SupraCoNeX/SupraCoNeX_3D_outdoor_enclosure_OpenWrt_Router/src/step/scnx_pigtail_bracket_9hole.step

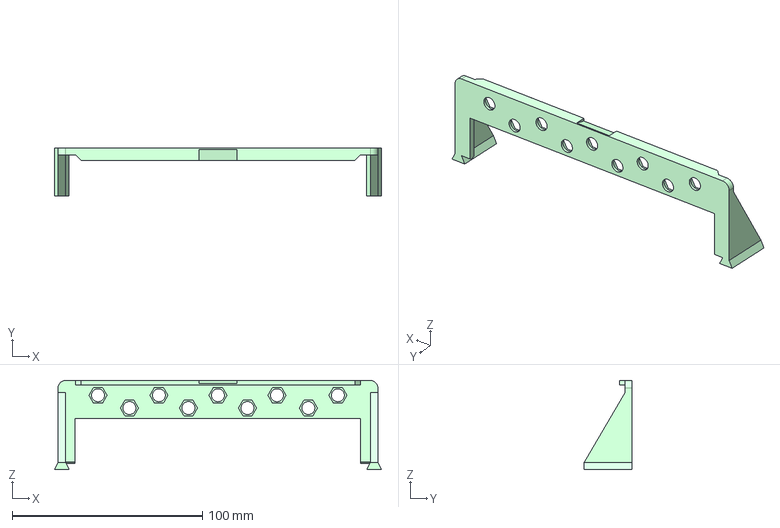
[picture p15: CAD file, 2021-03-08]
src/step/scnx_pigtail_bracket_9hole.step
171.8 x 25.0 x 46.8 mm
