SupraCoNeX/SupraCoNeX_3D_outdoor_enclosure_OpenWrt_Router/src/3mf/scnx_housing_ Boden_2.1_reinforced_pole_triangles.3mf

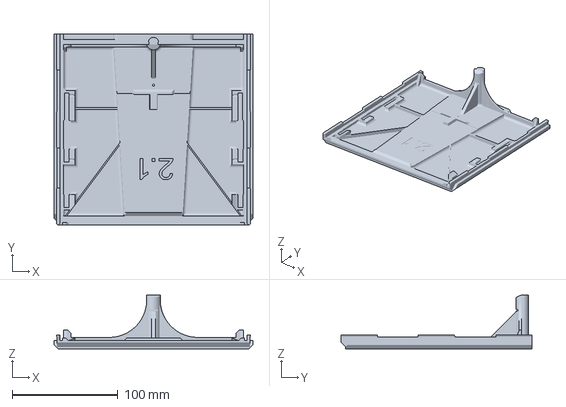
[picture p16: CAD file, 2023-10-01]
src/3mf/scnx_housing_ Boden_2.1_reinforced_pole_triangles.3mf
188.0 x 180.0 x 51.0 mm
