SupraCoNeX/SupraCoNeX_3D_outdoor_enclosure_OpenWrt_Router/src/3mf/scnx_internal_antenna_table_ears.3mf

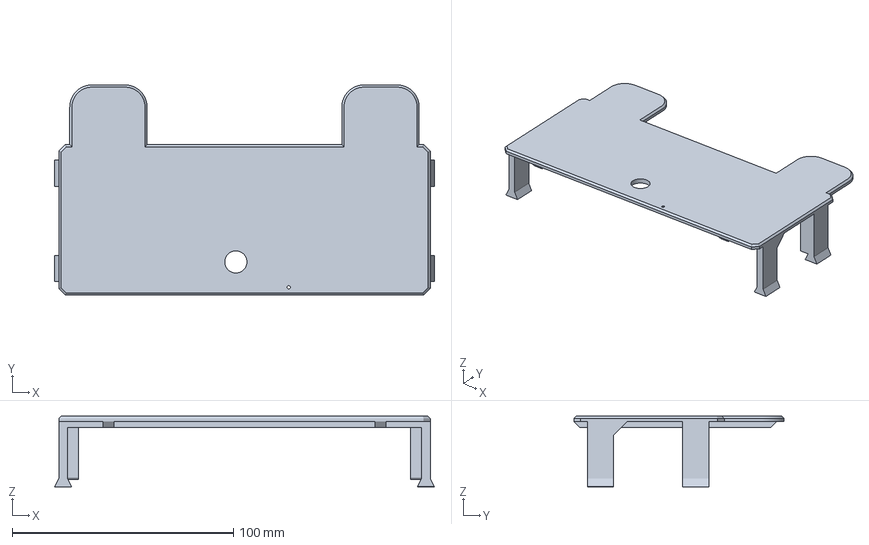
[picture p17: CAD file, 2023-04-04]
src/3mf/scnx_internal_antenna_table_ears.3mf
171.8 x 95.0 x 31.9 mm
