SupraCoNeX/SupraCoNeX_3D_outdoor_enclosure_OpenWrt_Router/src/step/scnx_internal_antenna_table.step

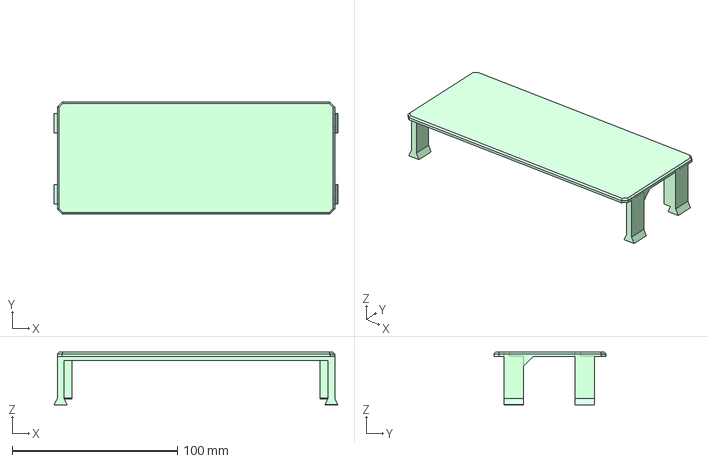
[picture p18: CAD file, 2021-03-08]
src/step/scnx_internal_antenna_table.step
171.9 x 68.0 x 31.9 mm
