SupraCoNeX/SupraCoNeX_3D_outdoor_enclosure_OpenWrt_Router/src/3mf/scnx_housing_wall_pole_mount_35.3mf

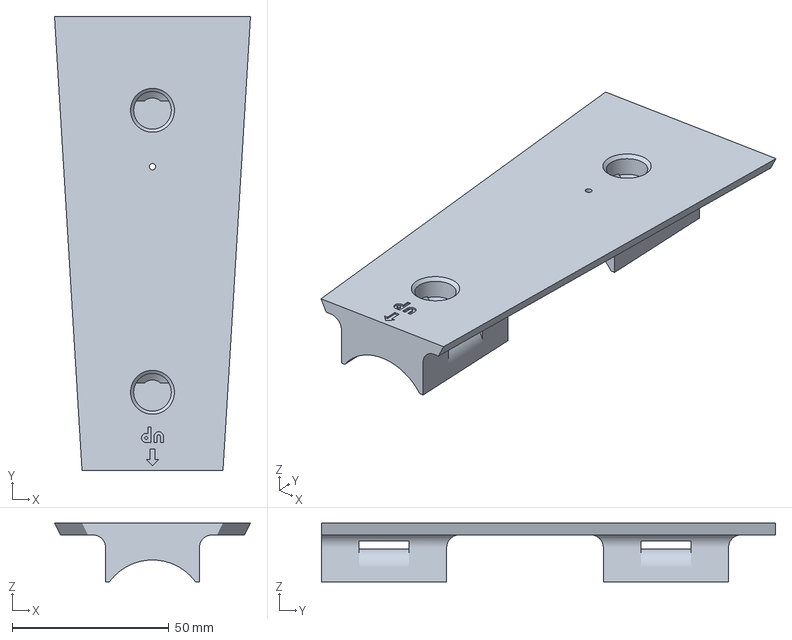
[picture p19: CAD file, 2023-03-25]
src/3mf/scnx_housing_wall_pole_mount_35.3mf
62.6 x 145.0 x 18.8 mm
