SupraCoNeX/SupraCoNeX_3D_outdoor_enclosure_OpenWrt_Router/src/3mf/scnx_top_cover_waterlip.3mf

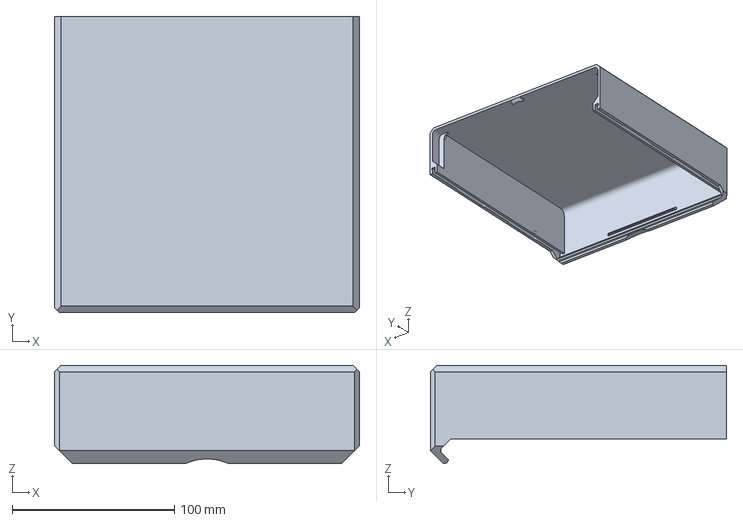
[picture p20: CAD file, 2023-03-25]
src/3mf/scnx_top_cover_waterlip.3mf
188.0 x 182.6 x 60.6 mm
