SupraCoNeX/SupraCoNeX_3D_outdoor_enclosure_OpenWrt_Router/src/step/scnx_splash_guard.step

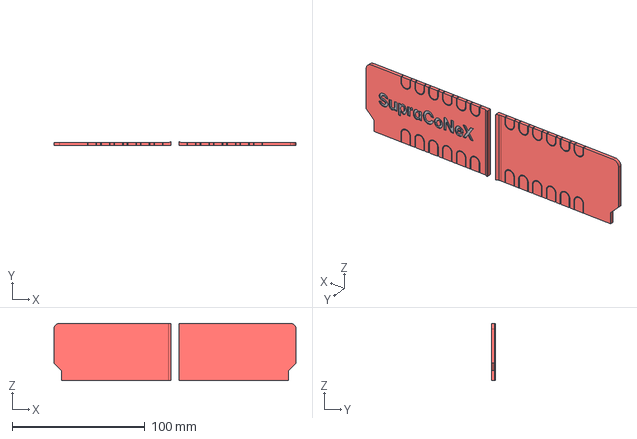
[picture p21: CAD file, 2021-02-12]
src/step/scnx_splash_guard.step
182.4 x 3.20 x 43.0 mm
