SupraCoNeX/SupraCoNeX_3D_outdoor_enclosure_OpenWrt_Router/src/step/scnx_pcb_mounting_plate.step

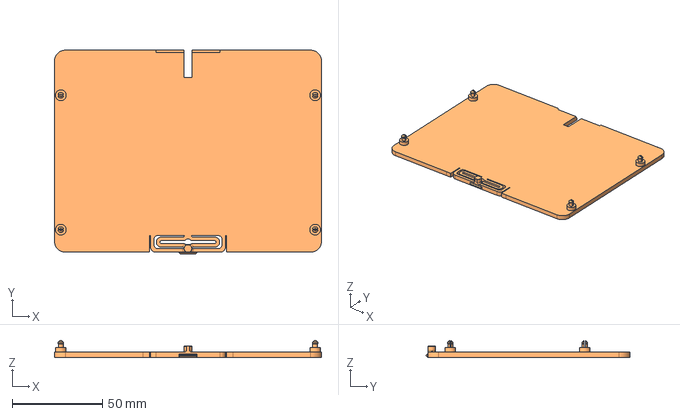
[picture p22: CAD file, 2021-02-12]
src/step/scnx_pcb_mounting_plate.step
148.0 x 112.9 x 9.50 mm
