SupraCoNeX/SupraCoNeX_3D_outdoor_enclosure_OpenWrt_Router/src/step/scnx_logo_letters.step

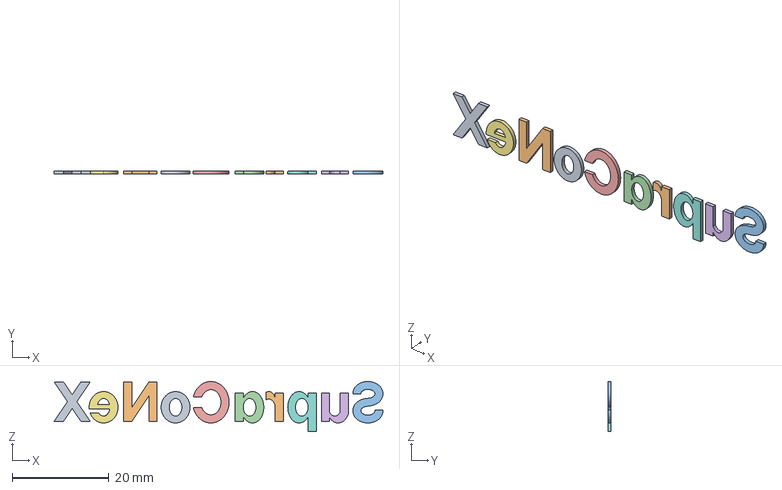
[picture p23: CAD file, 2021-02-12]
src/step/scnx_logo_letters.step
68.0 x 0.7 x 10.3 mm
