SupraCoNeX/SupraCoNeX_3D_outdoor_enclosure_OpenWrt_Router/src/3mf/scnx_housing_wall_pole_mount_50_2.0.3mf

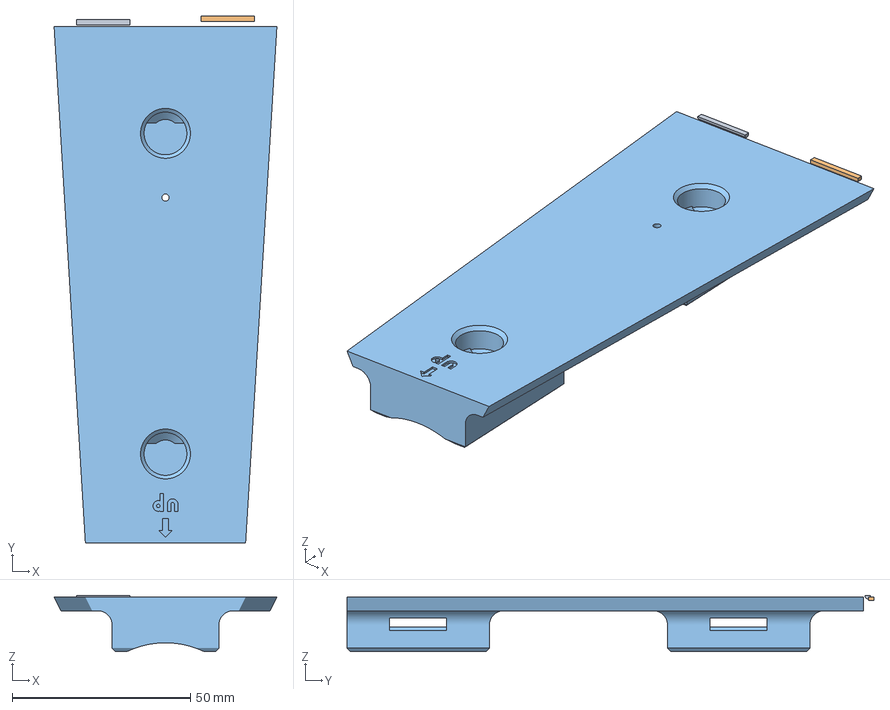
[picture p24: CAD file, 2022-07-11]
src/3mf/scnx_housing_wall_pole_mount_50_2.0.3mf
62.6 x 148.0 x 15.9 mm
wall_pole_mount_50
