SupraCoNeX/SupraCoNeX_3D_outdoor_enclosure_OpenWrt_Router/src/3mf/scnx_ball_mount_v3.3mf

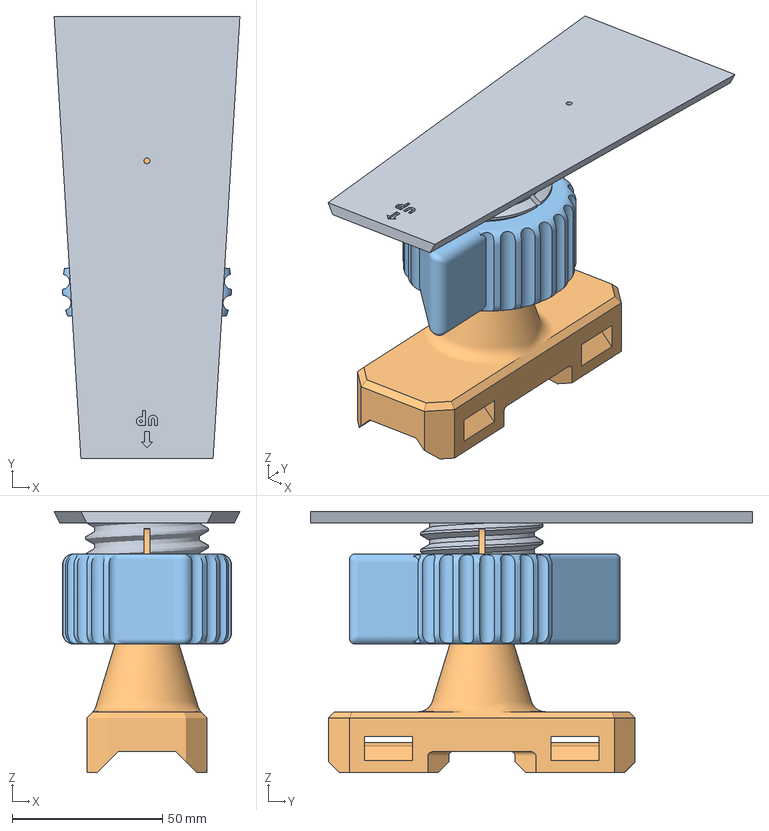
[picture p25: CAD file, 2022-03-20]
src/3mf/scnx_ball_mount_v3.3mf
61.8 x 147.0 x 86.8 mm
base_pot
ball
screw
