SupraCoNeX/SupraCoNeX_3D_outdoor_enclosure_OpenWrt_Router/src/3mf/scnx_internal_antenna_pole_R.3mf

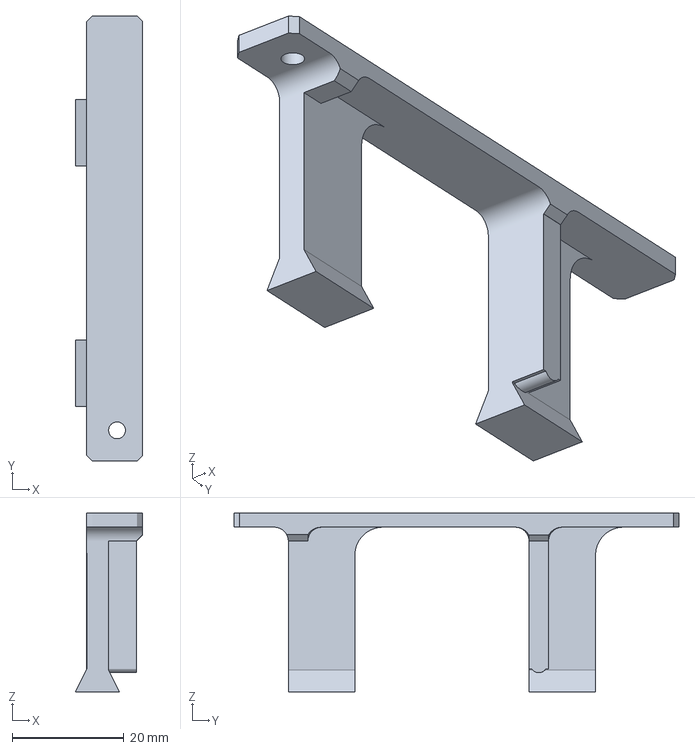
[picture p26: CAD file, 2022-03-20]
src/3mf/scnx_internal_antenna_pole_R.3mf
12.0 x 79.5 x 31.9 mm
